WeatherlyMed/BrokeCW/antenna/IMG_20240729_161805708.jpg

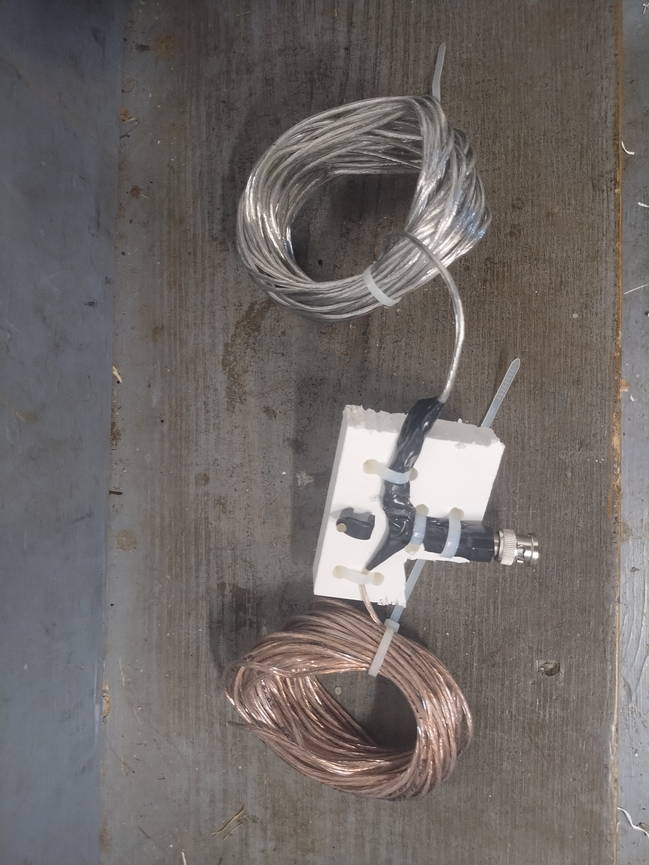
antenna/IMG_20240729_161805708.jpg
