WeatherlyMed/BrokeCW/antenna/IMG_20240731_103034649.jpg

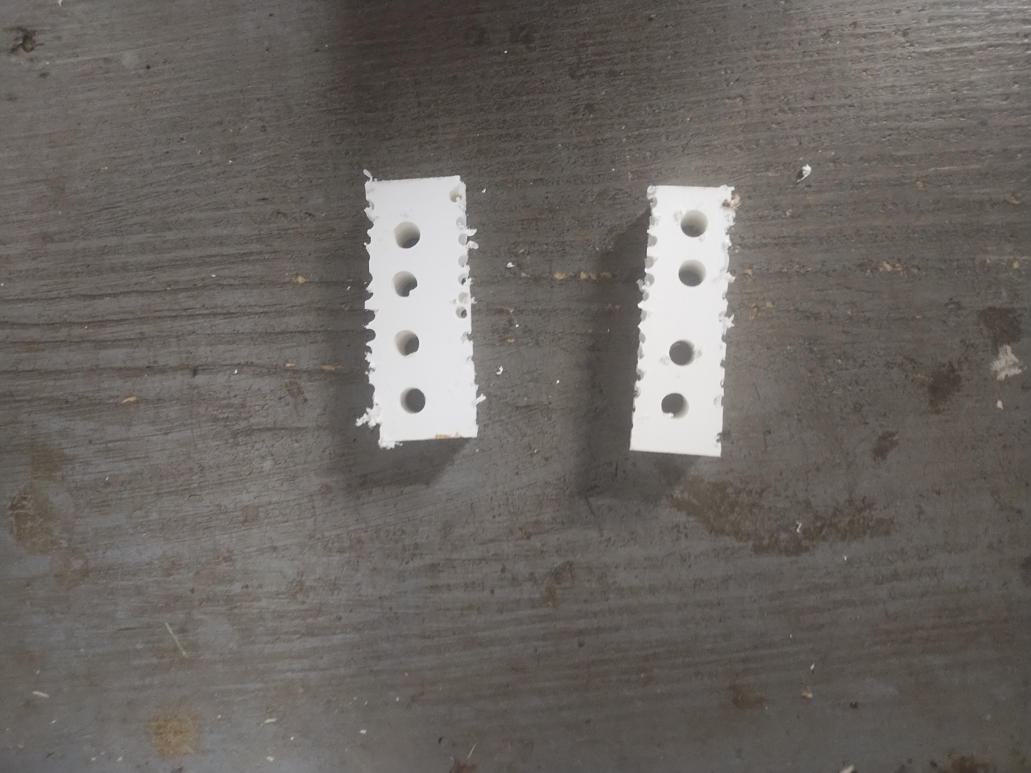
antenna/IMG_20240731_103034649.jpg
