WeatherlyMed/BrokeCW/artifact/IMG_20240728_195354976.jpg

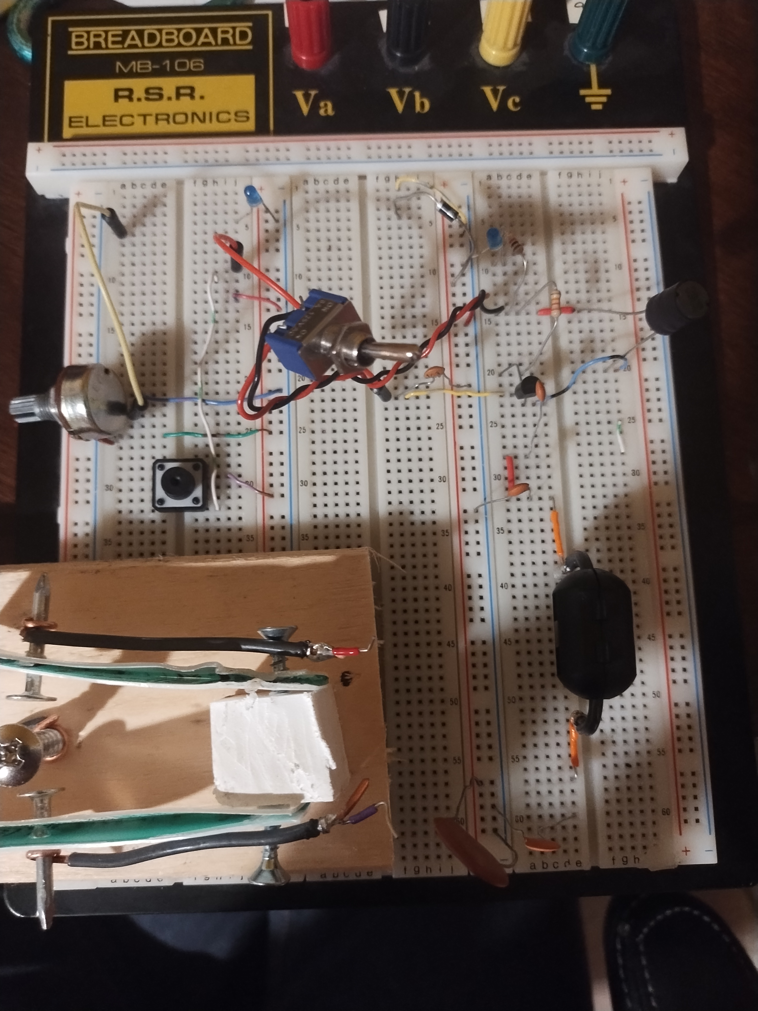
artifact/IMG_20240728_195354976.jpg
