WeatherlyMed/BrokeCW/artifact/IMG_20240728_210127684_HDR.jpg

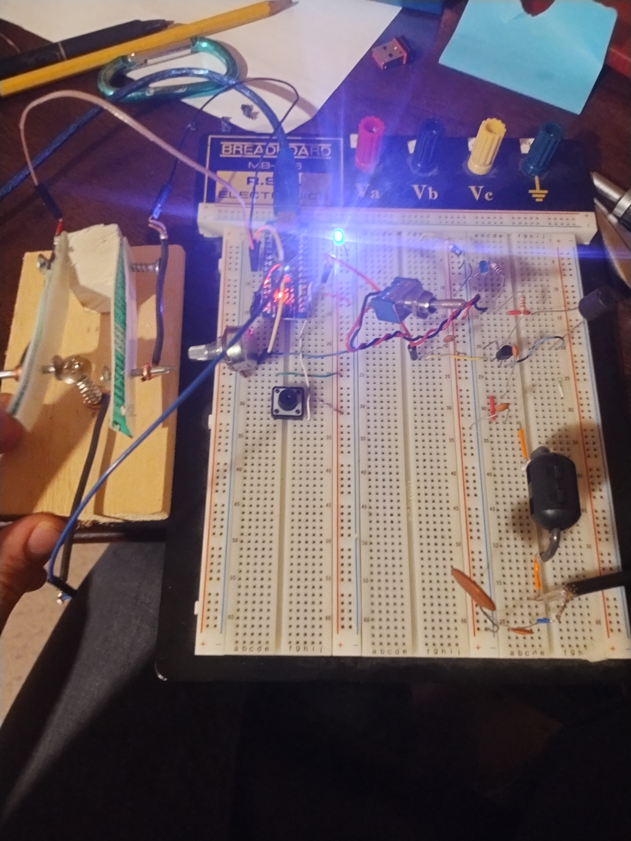
artifact/IMG_20240728_210127684_HDR.jpg
