WeatherlyMed/BrokeCW/artifact/IMG_20240807_232231078.jpg

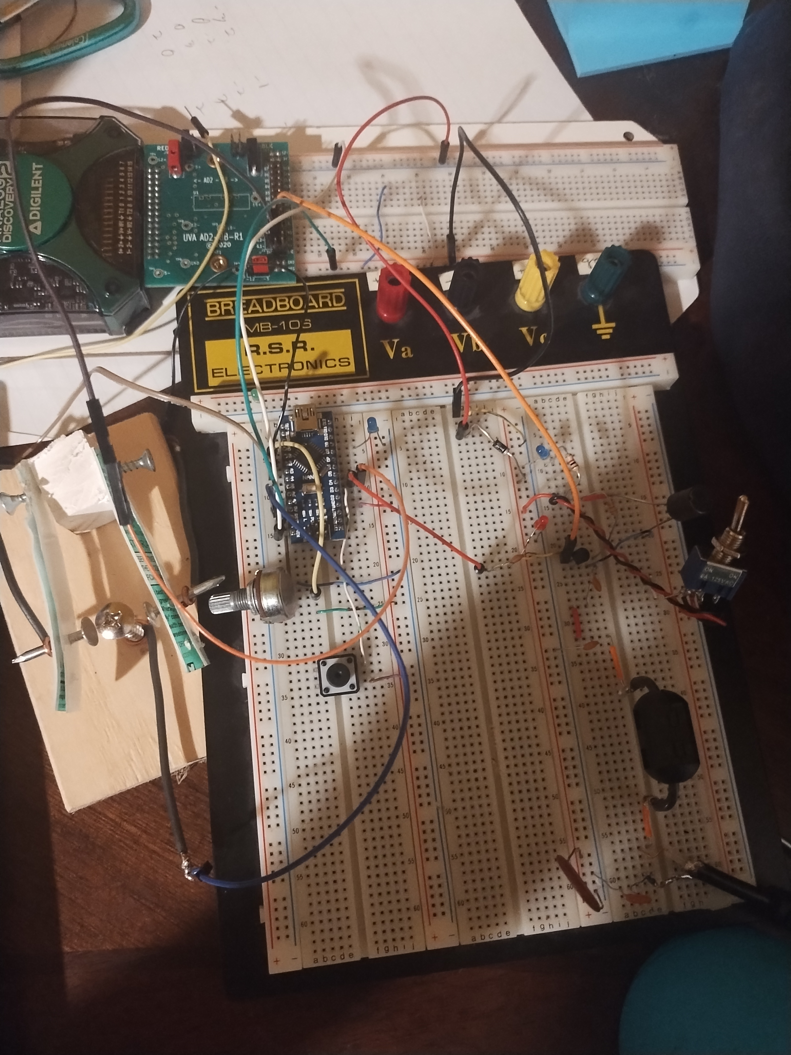
artifact/IMG_20240807_232231078.jpg
