WeatherlyMed/BrokeCW/keyer/IMG_20240815_001016121.jpg

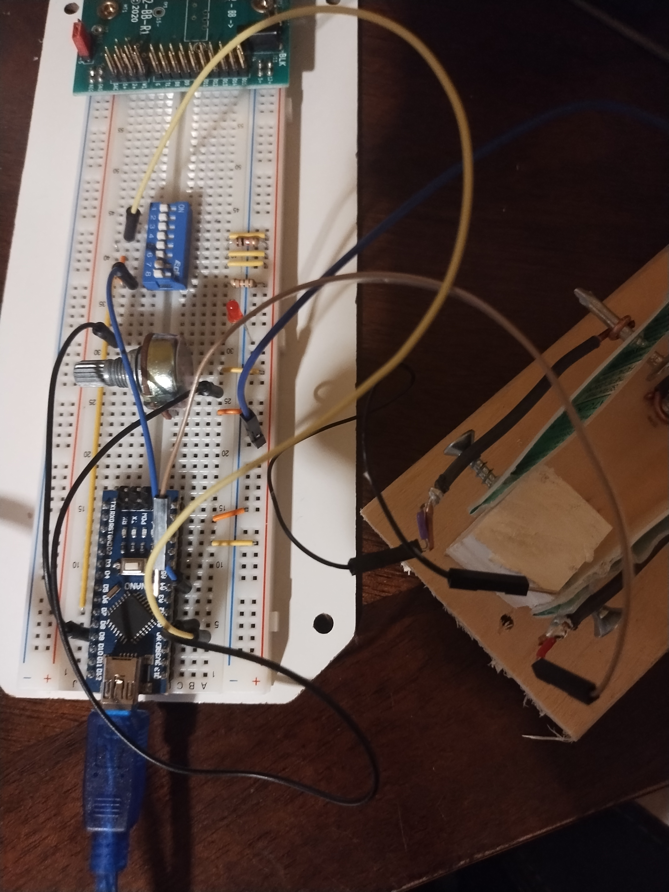
keyer/IMG_20240815_001016121.jpg
