WeatherlyMed/BrokeCW/receiver/IMG_20240808_172011317~2.jpg

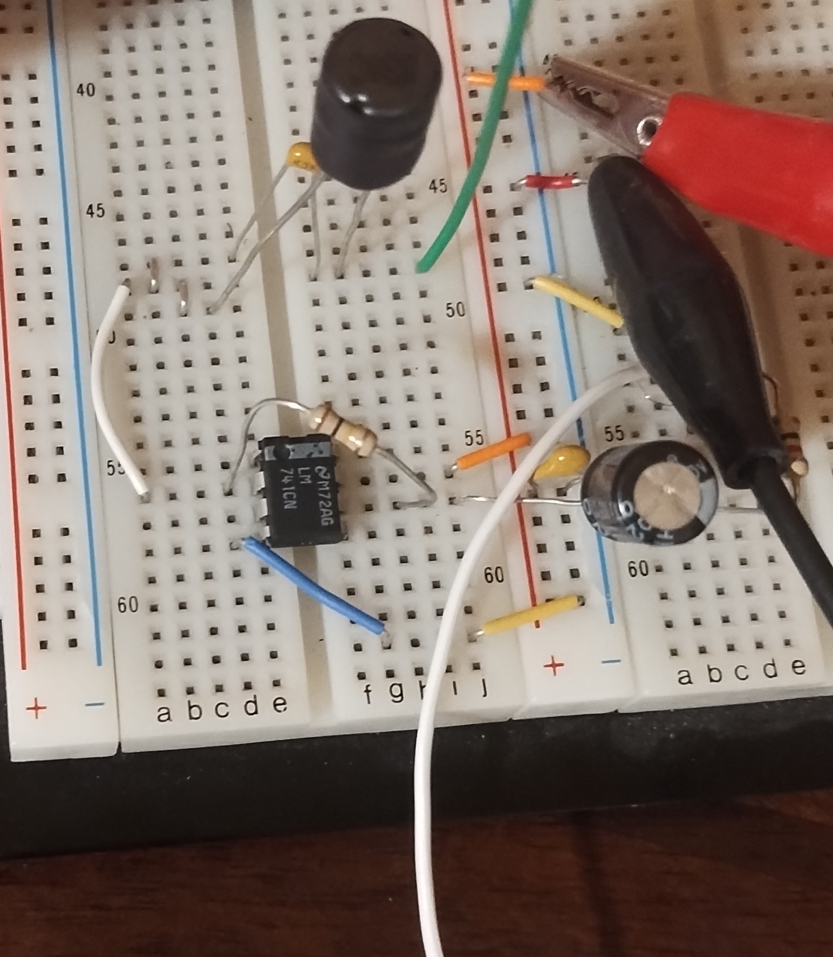
receiver/IMG_20240808_172011317~2.jpg
