WeatherlyMed/BrokeCW/receiver/testing/IMG_20240809_094516433.jpg

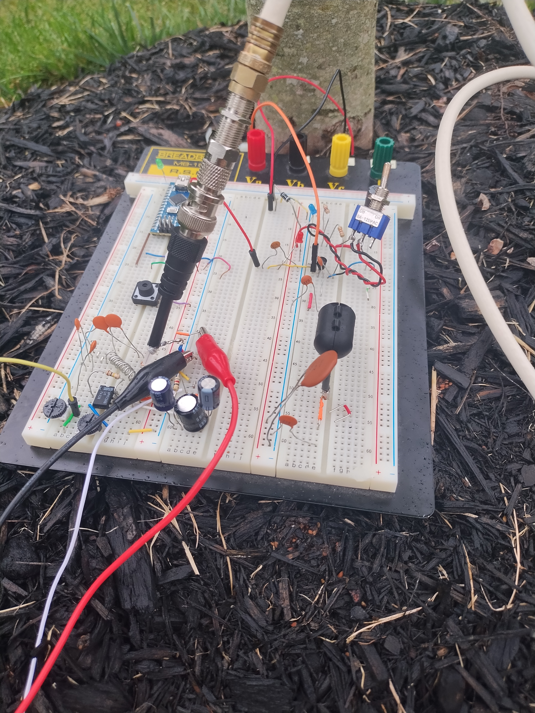
receiver/testing/IMG_20240809_094516433.jpg
